tmsaavedra/wateringsystem/IMG74.jpeg

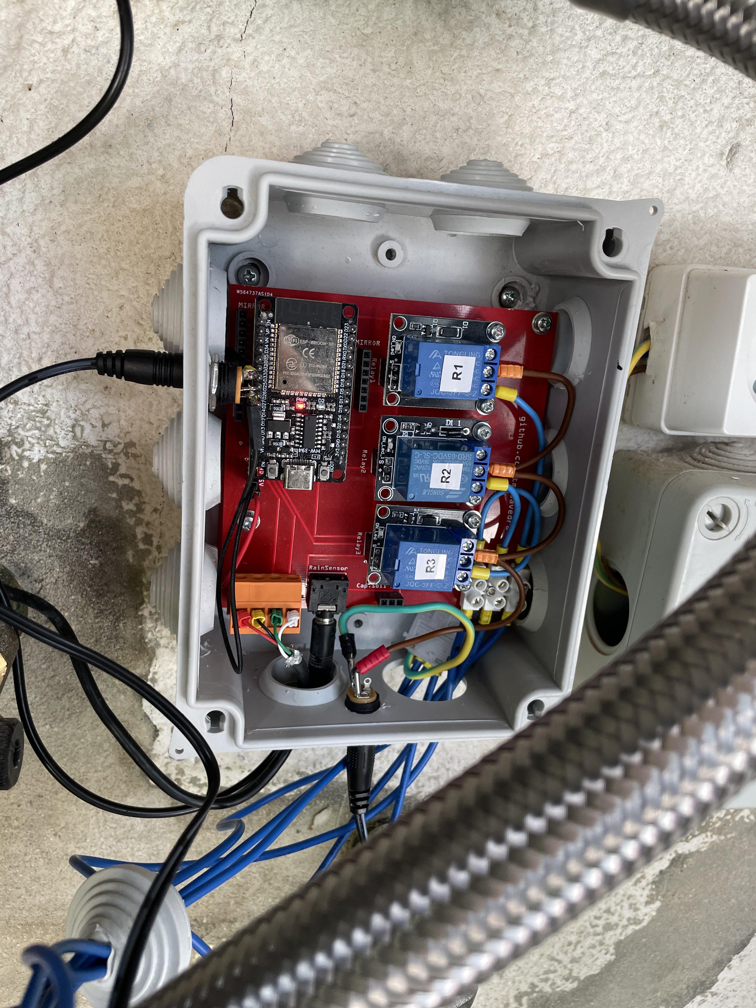
IMG74.jpeg
