tmsaavedra/wateringsystem/IMG77.jpeg

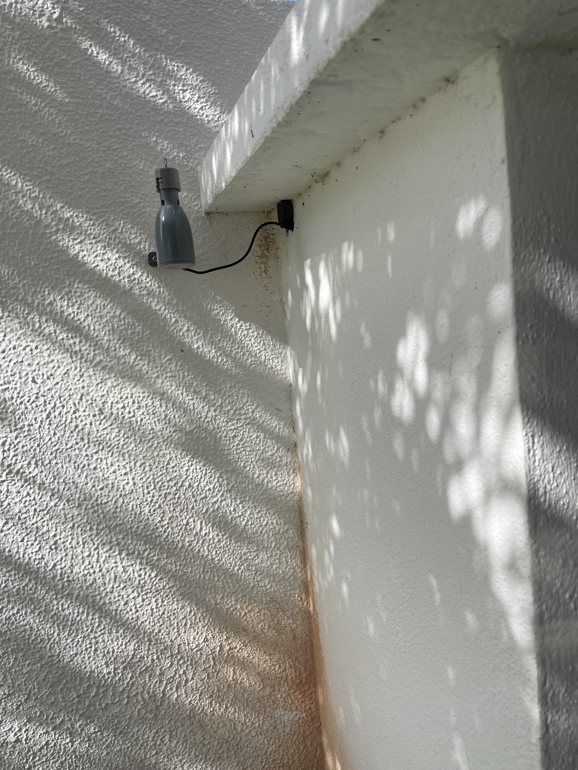
IMG77.jpeg
